pbosio72/Siemens-M-Pulse-Repeater-Interface/technics/pinout/Pinout_Attuation.xls

Sheet: PinOut
Component | Colore | Color | Pin N° | Switch | Note
Relé 1 | Verde/Verde scuro | Green/Dark Green | 6 |  | Scrittura disco / Write disk
 | Azzurro | Blue | 1
 | Azzurro | Blue | 1
Relé | Verde | Green | 5 |  | Ruota testina senso antiorario / Anti-clockwise head rotation
 | Azzurro | Blue | 1
Relé 3 | Rosso/Grigio | Red/Gray | 2 |  | Ruota testina senso orario / Clockwise head rotation
 | Azzurro | Blue | 1
 | Azzurro | Blue | 1
Multi Switch 1 | Rosa | Pink | 24 | A
 | Verde/Marrone | Green/Brown | 20 | A
 | Blu/Marrone | Blue/Brown | 16 | B
 | Giallo/Marrone | Yellow/Brown | 12 | B
 | Bianco/Verde | White/Green | 11 | C
 | Blu/Verde | Blue/Green | 15 | C
 | Giallo/Bianco | Yellow/White | 19 | I | Testina di lettura (reading head)
 | Nero/Bianco | Black/White | 23 | I | OFF → open / ON R=168 ohm
Multi Switch 2 | Nero/Marrone | Black/Brown | 4 | D
 | Marrone | Brown | 8 | D
 | Bianco/Verde | White/Green | 7 | E
 | Nero | Black | 3 | E
Multi Switch 3 | Rosso/Nero | Red/Black | 18 | F
 | Giallo/Nero | Yellow/Black | 22 | F
 | Giallo | Yellow | 17 | F
Multi Switch 4 | Bianco/Rosso | White/Red | 10 | G
 | Grigio/Rosso | Gray/Red | 14 | G
 | Grigio | Gray | 9 | H
 | Rosa | Pink | 13 | H
Pin 21 non trovato / not found

Sheet: Relé actuation
 | Relé 1 | OFF | ON
Multi Switch 4 | G (10-14) | OFF | ON
 | H (9-13) | OFF | ON
 | Relé 2 | OFF | ON
Multi Switch 2 | D (4-8) | ON | OFF
 | E (7-3) | OFF | ON
 | Relé 3 | OFF | ON
Multi Switch 3 | F (18-22) | OFF | ON
 | F (17-22) | ON | OFF
 | R | V measured | I=V/R | I measured
 | [ohm] | [V] | [mA] | [mA]
Relé 1 | 822 | 49.23 | 59.89 | 61
Relé 2 | 603 | 49.23 | 81.64 | 82
Relé 3 | 315.6 | 49.23 | 155.99 | 155

Sheet: Disc rotation
 |  | Disco ruotato tutto in senso orario | Disco in rotazione | Disco ruotato tutto in senso antiorario
 |  | Disc rotated fully clockwise | Disc rotating | Disc rotated fully counterclockwise
Multi Switch 1 | A (20-24) | OFF | ON | ON
 | B (16-12) | OFF | OFF | ON
 | C (11-14) | ON | ON | OFF
