pbosio72/Siemens-M-Pulse-Repeater-Interface/arduino/examples/1_Buttons_activation/Circuit_scheme_schem.jpg

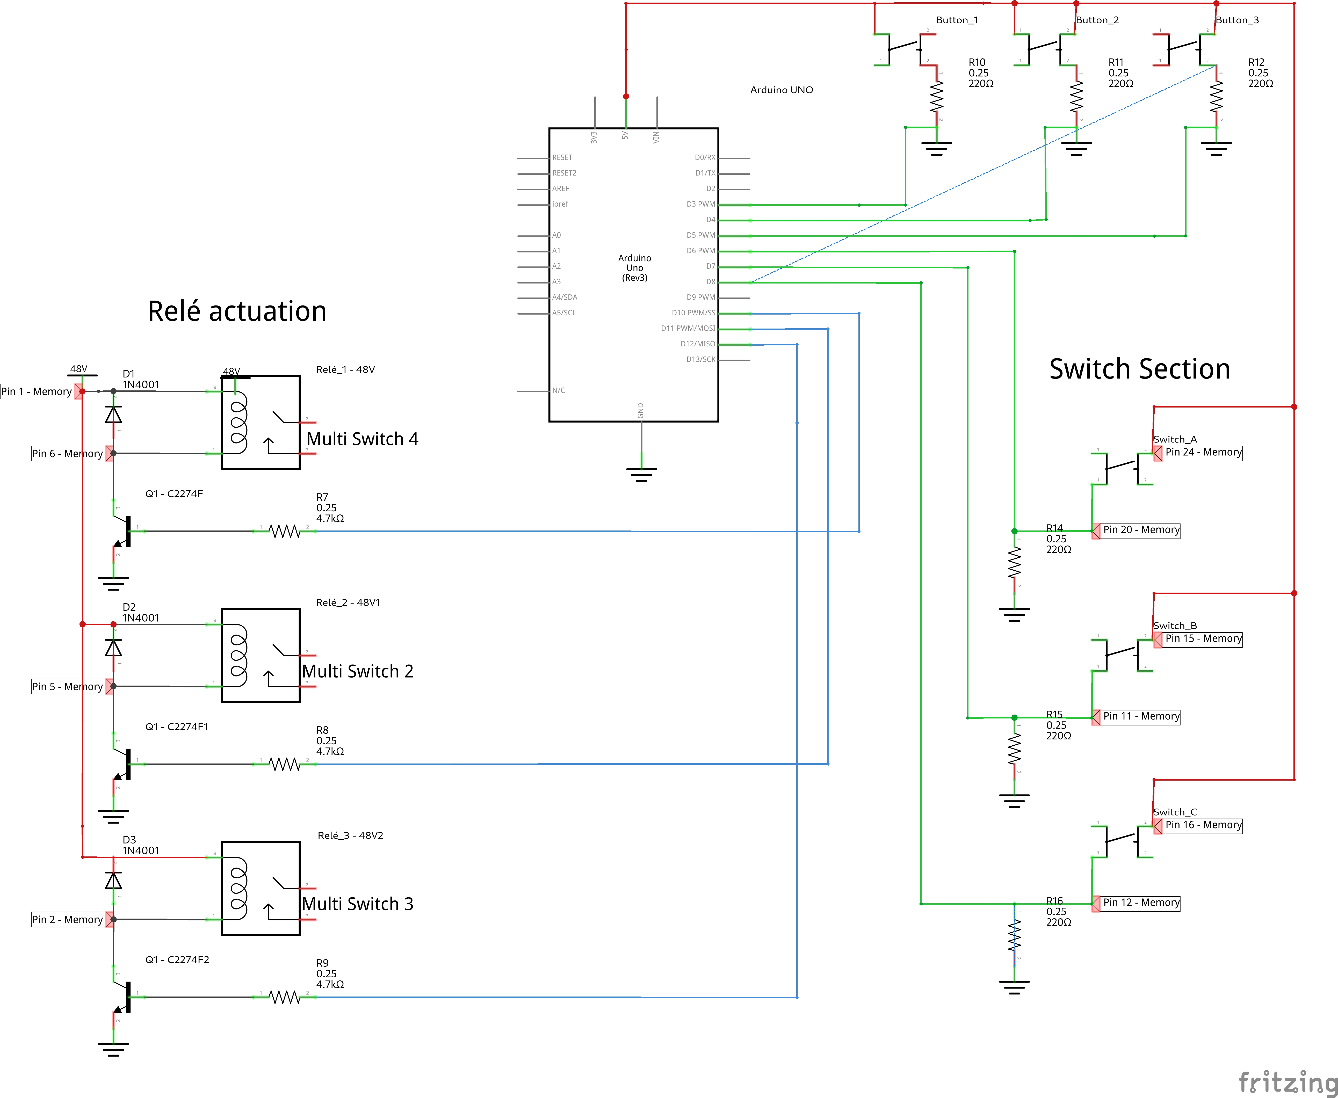
arduino/examples/1_Buttons_activation/Circuit_scheme_schem.jpg
