pbosio72/Siemens-M-Pulse-Repeater-Interface/arduino/examples/8_write_read_display_keypad_PCF8574/Circuit_scheme.jpg

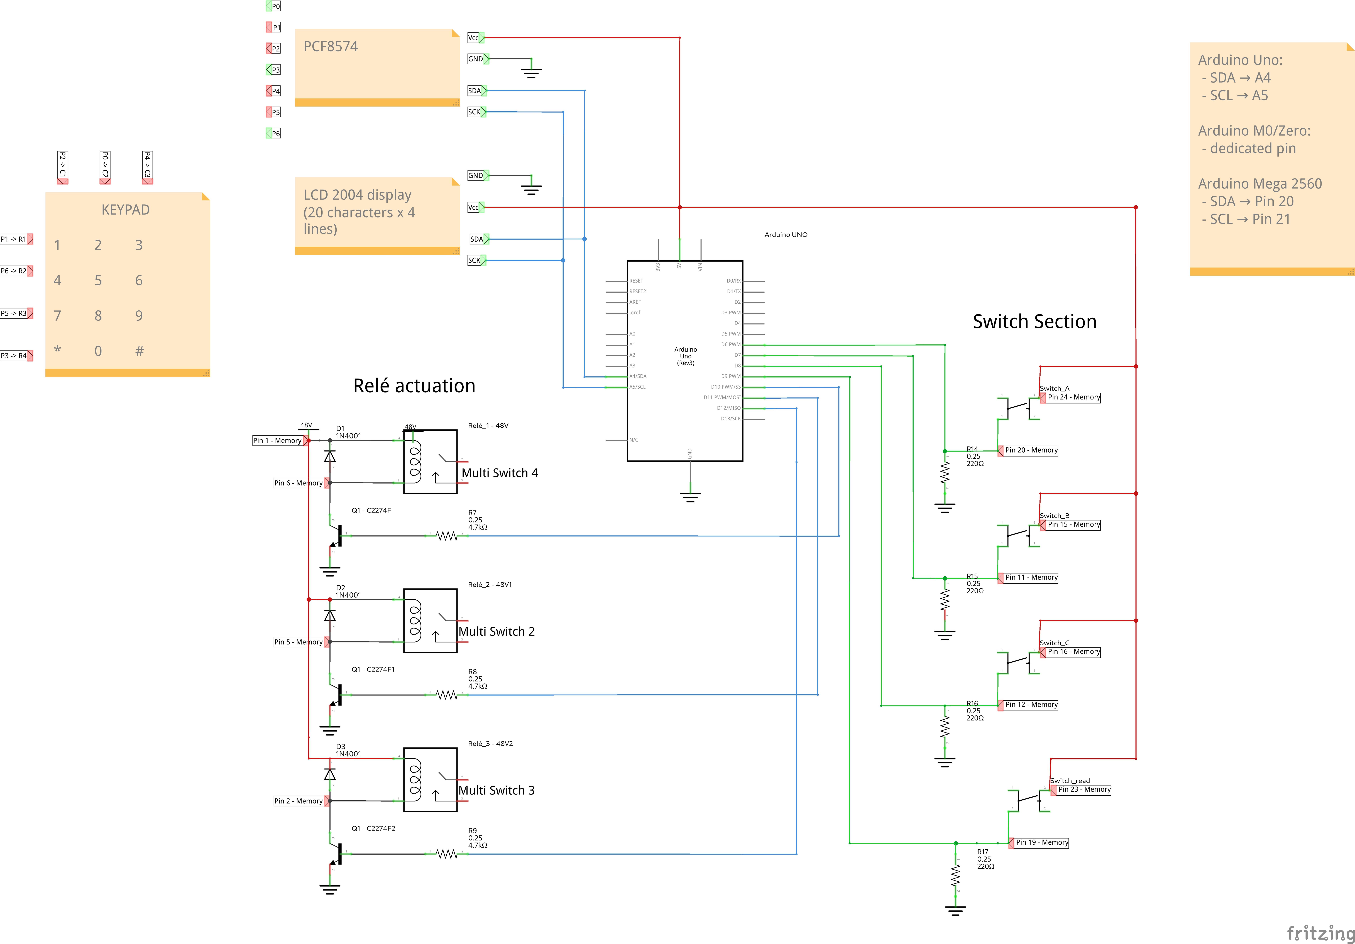
arduino/examples/8_write_read_display_keypad_PCF8574/Circuit_scheme.jpg
