pbosio72/Siemens-M-Pulse-Repeater-Interface/photos/Rele_3-MultiSwitch_3.jpg

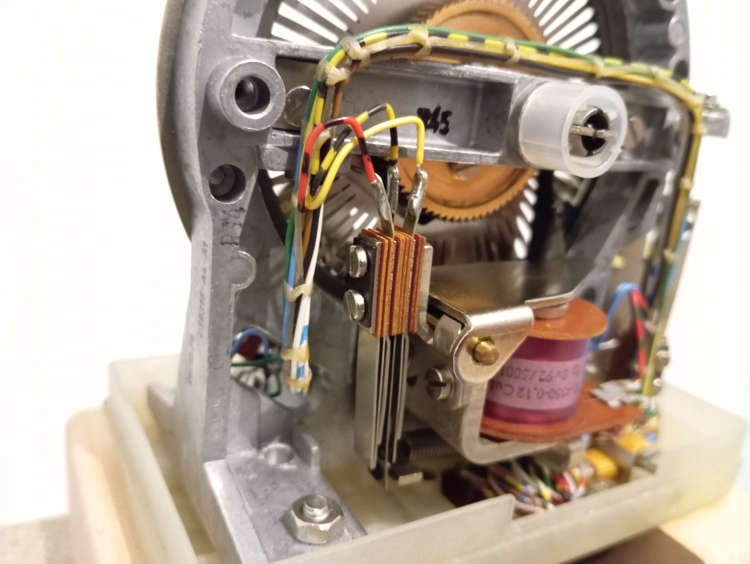
photos/Rele_3-MultiSwitch_3.jpg
