pbosio72/Siemens-M-Pulse-Repeater-Interface/arduino/examples/Utility_01_LCD_address/Utility_01_LCD_address.ino

#include <Wire.h>
// The purpose of the sketch is to display in the serial monitor the
// right LCD address

void setup() {
  Wire.begin();
  Serial.begin(9600);
  Serial.println("I2C Scanner");
}

void loop() {
  byte error, address;
  int nDevices;
  
  Serial.println("Scanning...");
  nDevices = 0;
  
  for(address = 1; address < 127; address++) {
    Wire.beginTransmission(address);
    error = Wire.endTransmission();
    
    if (error == 0) {
      Serial.print("Device found at 0x");
      if (address < 16) Serial.print("0");
      Serial.println(address, HEX);
      nDevices++;
    }
  }
  
  if (nDevices == 0)
    Serial.println("No I2C devices found");
  else
    Serial.println("Done");
    
  delay(5000);
}
